Yasu31/Mini-Mobile-Manipulator/catkin_ws/src/mayfes/bot/img/0.jpg

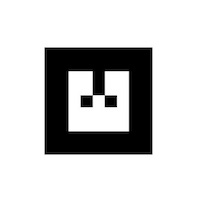
catkin_ws/src/mayfes/bot/img/0.jpg
