Yasu31/Mini-Mobile-Manipulator/catkin_ws/src/mayfes/bot/img/1.jpg

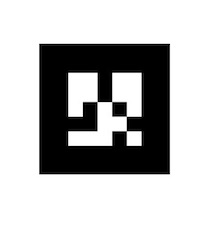
catkin_ws/src/mayfes/bot/img/1.jpg
