Yasu31/Mini-Mobile-Manipulator/img/ICS_connect.png

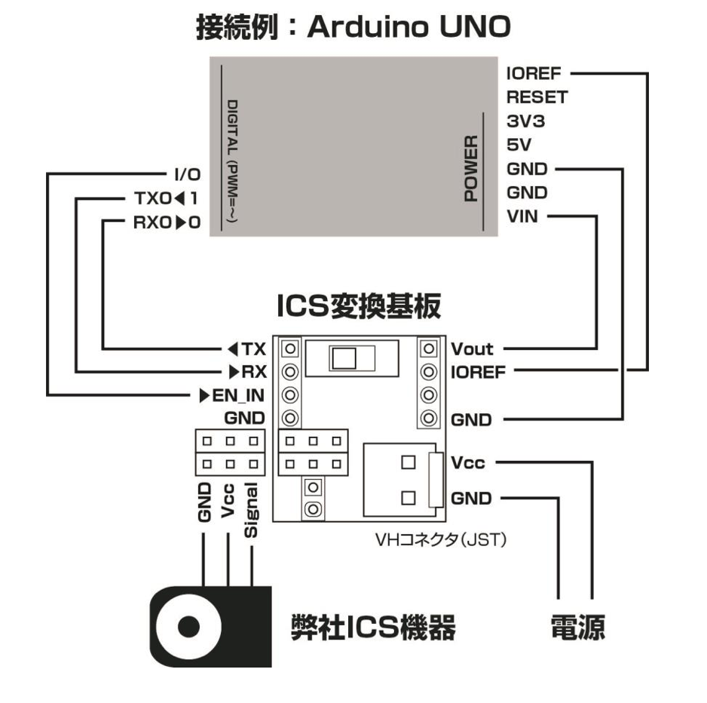
img/ICS_connect.png
