Yasu31/Mini-Mobile-Manipulator/img/IMG_5229.png

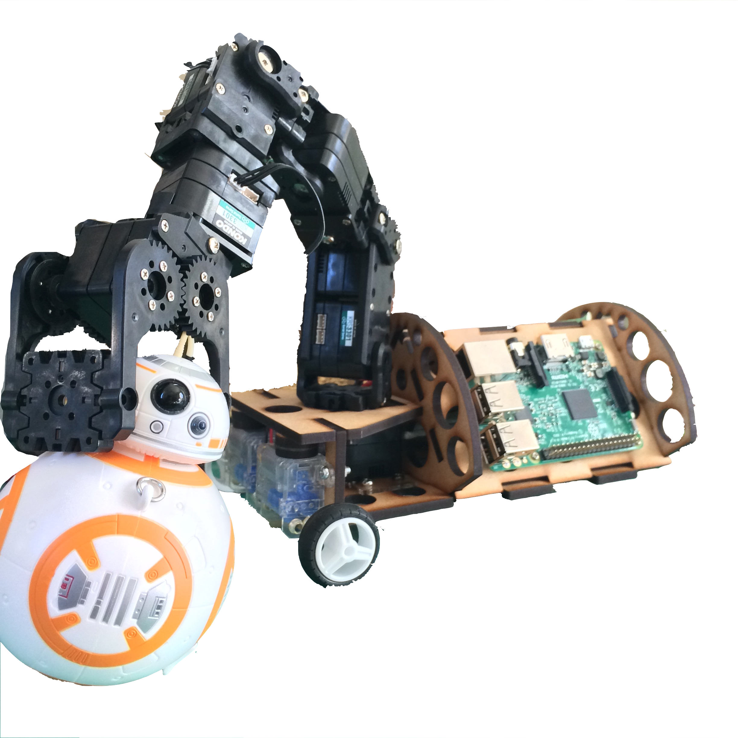
img/IMG_5229.png
