Yasu31/Mini-Mobile-Manipulator/img/modelC_render.png

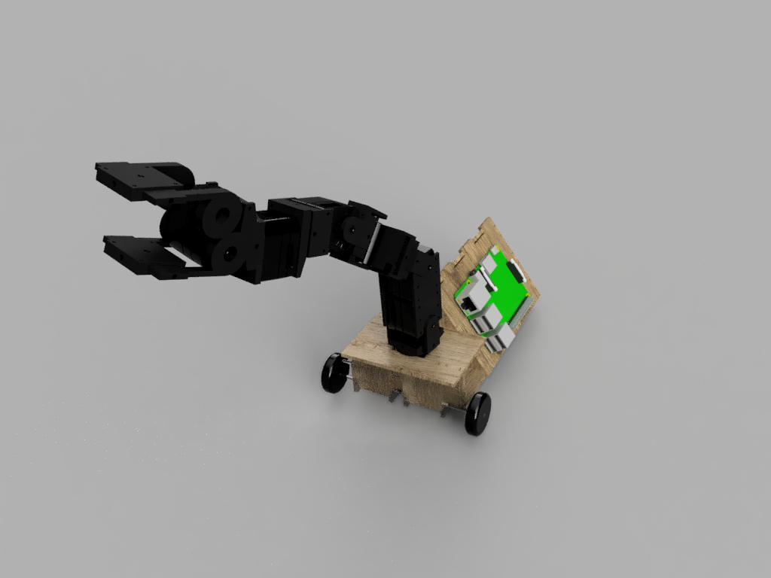
img/modelC_render.png
