Yasu31/Mini-Mobile-Manipulator/img/urdf_cad.png

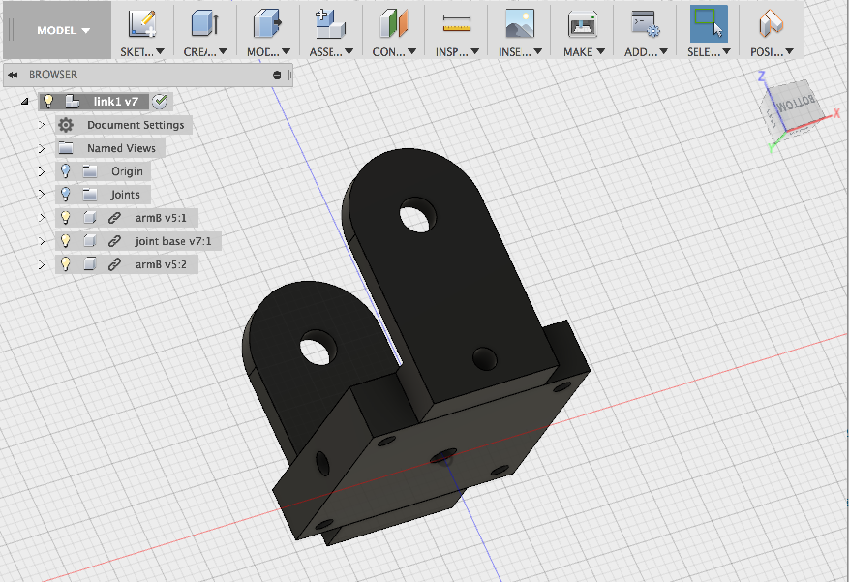
img/urdf_cad.png
