Yasu31/Mini-Mobile-Manipulator/Laser Cut Data/design C v1/rear wheel board.dxf

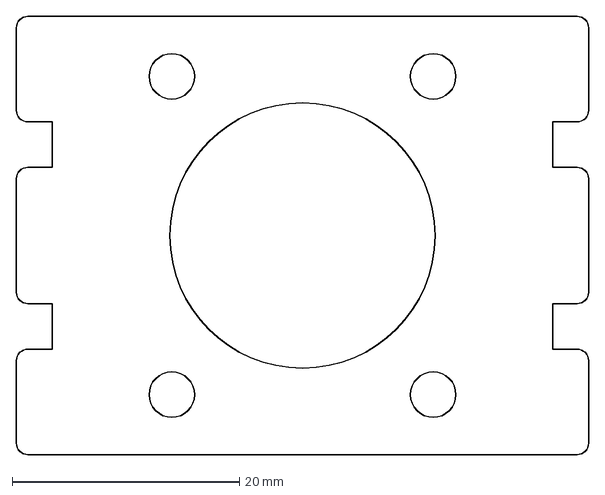
[picture p31: CAD file, 2017-12-26]
Laser Cut Data/design C v1/rear wheel board.dxf
50.3 x 38.6 mm
