Yasu31/Mini-Mobile-Manipulator/catkin_ws/src/mmm_description/meshes/Slink0.stl

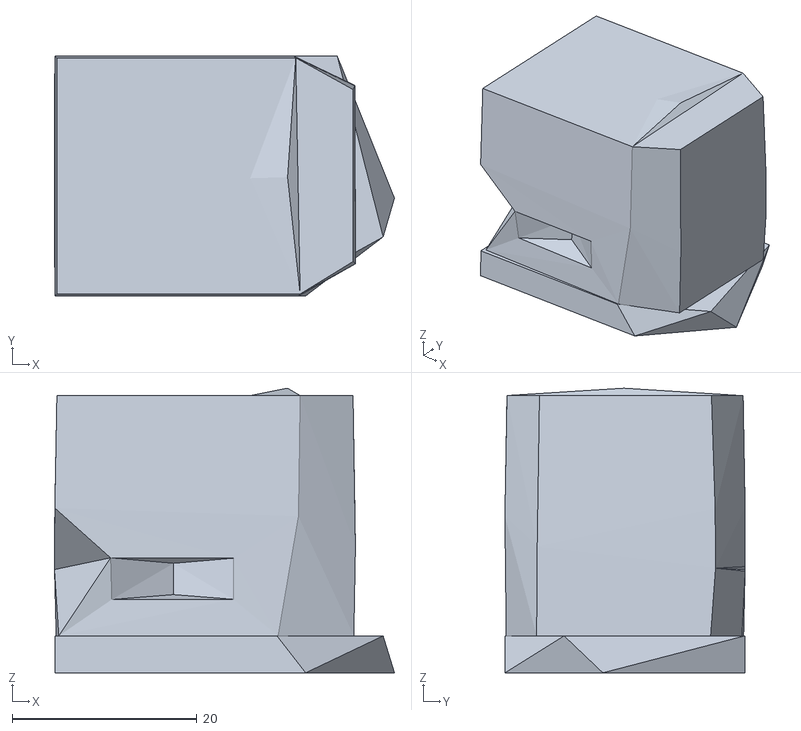
[picture p32: CAD file, 2018-01-10]
catkin_ws/src/mmm_description/meshes/Slink0.stl
36.8 x 26.0 x 30.8
