Yasu31/Mini-Mobile-Manipulator/Laser Cut Data/design C v1/middle board.dxf

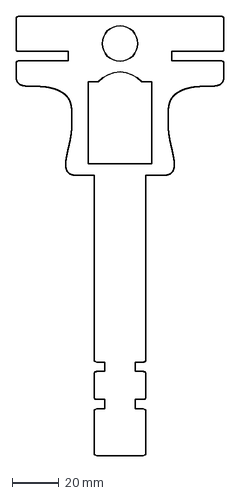
[picture p33: CAD file, 2017-12-26]
Laser Cut Data/design C v1/middle board.dxf
89.0 x 188.0 mm
