Yasu31/Mini-Mobile-Manipulator/catkin_ws/src/mmm_description/meshes/Slink7.stl

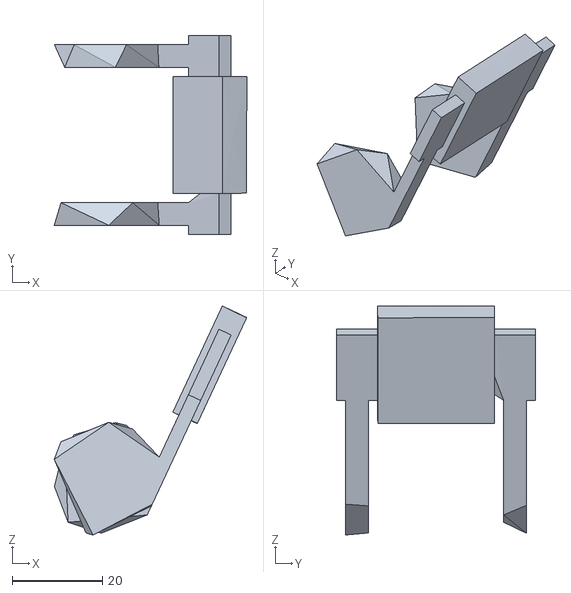
[picture p34: CAD file, 2018-01-10]
catkin_ws/src/mmm_description/meshes/Slink7.stl
42.7 x 44.0 x 50.7
