Yasu31/Mini-Mobile-Manipulator/Laser Cut Data/design C v1/diagonal board.dxf

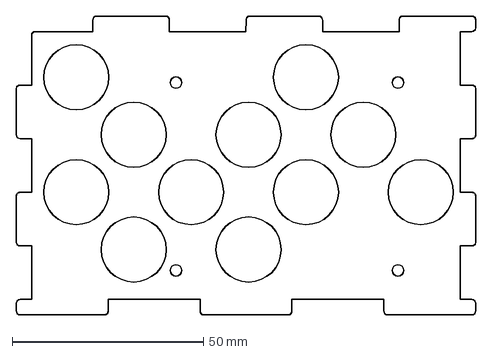
[picture p35: CAD file, 2017-12-26]
Laser Cut Data/design C v1/diagonal board.dxf
120.0 x 78.0 mm
