Yasu31/Mini-Mobile-Manipulator/catkin_ws/src/mmm_description/meshes/Slink5.stl

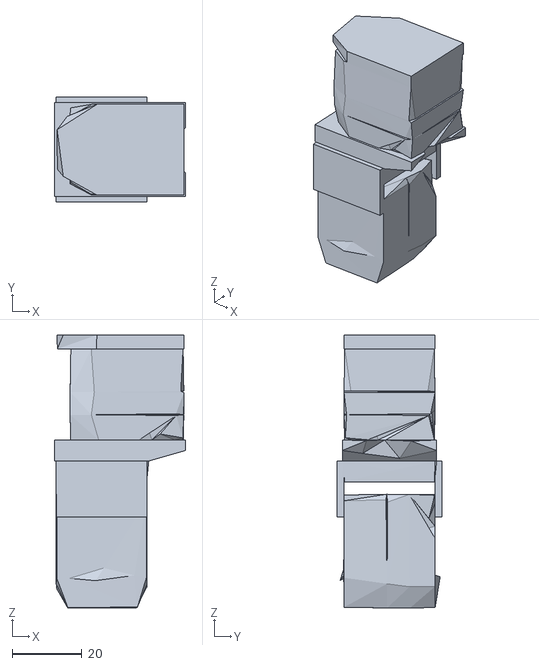
[picture p36: CAD file, 2018-01-10]
catkin_ws/src/mmm_description/meshes/Slink5.stl
37.5 x 30.0 x 78.0
