Yasu31/Mini-Mobile-Manipulator/catkin_ws/src/mmm_description/meshes/camera.stl

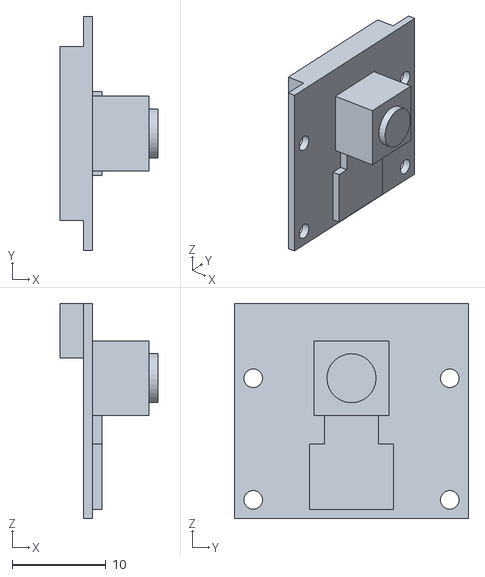
[picture p37: CAD file, 2018-01-08]
catkin_ws/src/mmm_description/meshes/camera.stl
10.5 x 25.0 x 23.0
