Yasu31/Mini-Mobile-Manipulator/catkin_ws/src/mmm_description/meshes/link7.stl

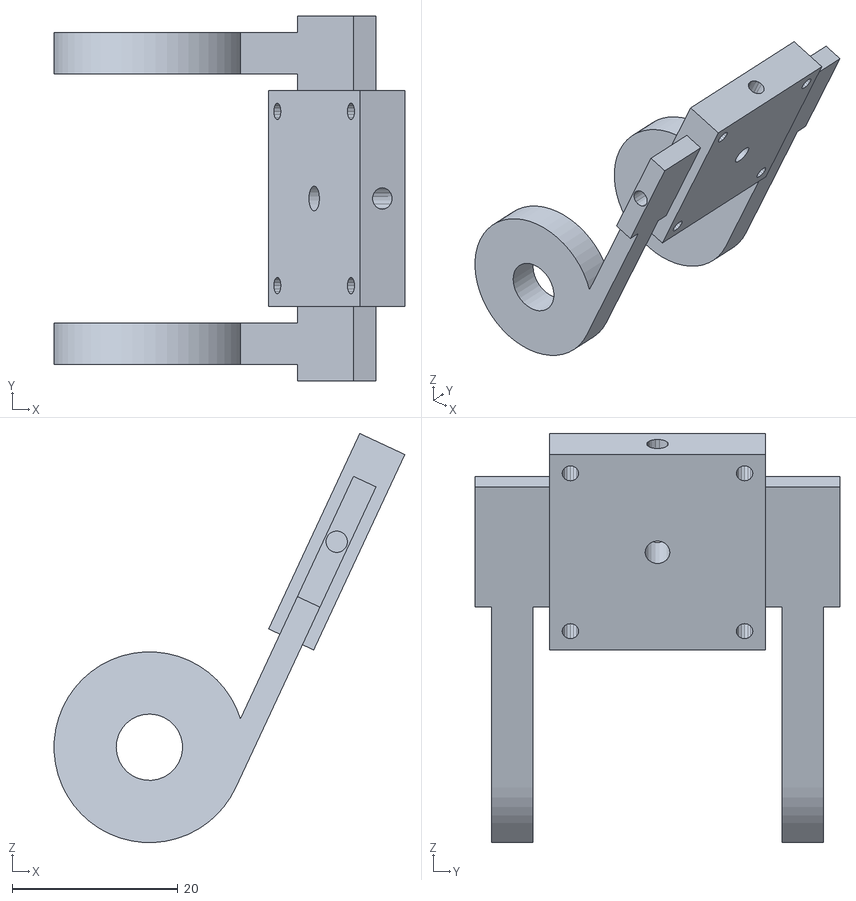
[picture p38: CAD file, 2018-01-02]
catkin_ws/src/mmm_description/meshes/link7.stl
42.3 x 44.0 x 49.3
