Yasu31/Mini-Mobile-Manipulator/catkin_ws/src/mmm_description/meshes/link6.stl

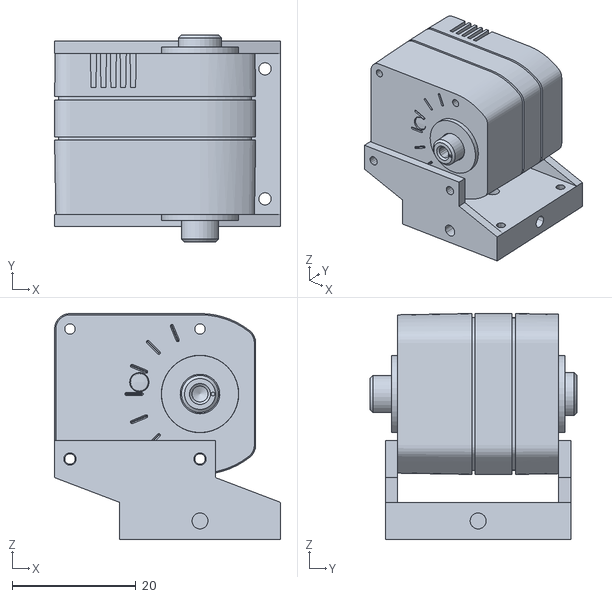
[picture p39: CAD file, 2018-01-02]
catkin_ws/src/mmm_description/meshes/link6.stl
36.5 x 33.5 x 36.5
