Yasu31/Mini-Mobile-Manipulator/catkin_ws/src/mmm_description/meshes/link2.stl

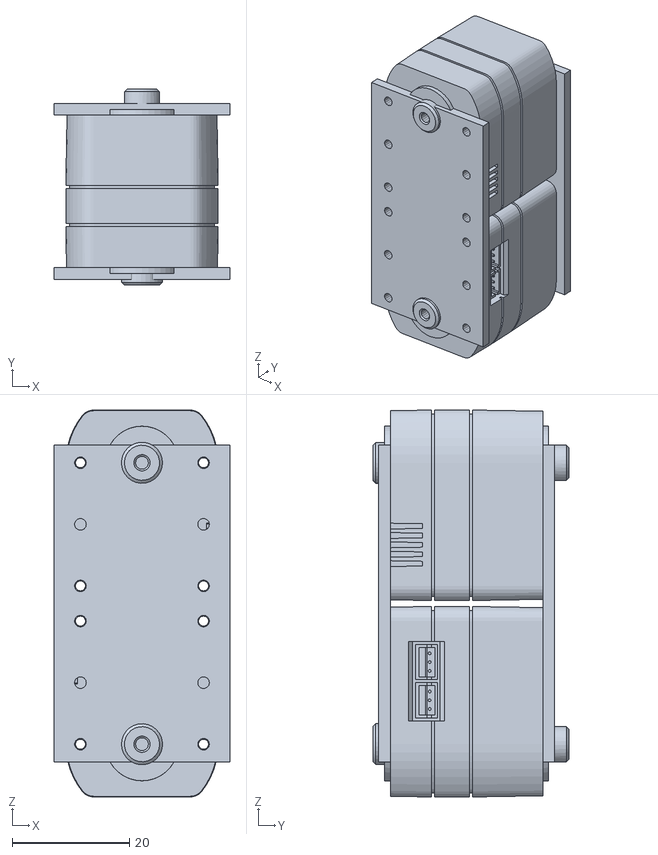
[picture p40: CAD file, 2017-12-29]
catkin_ws/src/mmm_description/meshes/link2.stl
30.0 x 33.5 x 66.0
