Yasu31/Mini-Mobile-Manipulator/catkin_ws/src/mmm_description/meshes/link4.stl

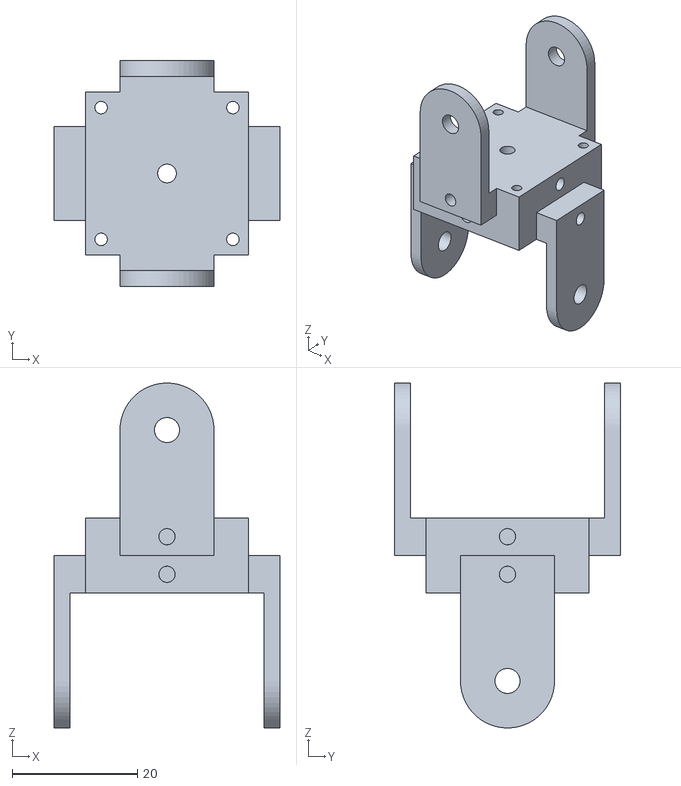
[picture p41: CAD file, 2017-12-29]
catkin_ws/src/mmm_description/meshes/link4.stl
36.0 x 36.0 x 55.0
