Yasu31/Mini-Mobile-Manipulator/catkin_ws/src/mmm_description/meshes/link5.stl

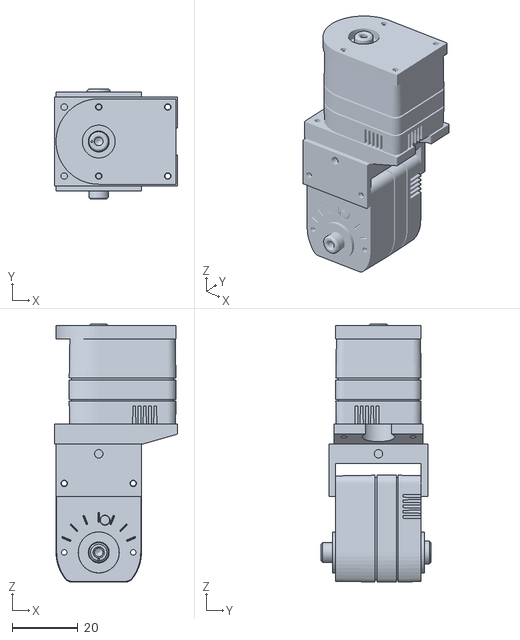
[picture p42: CAD file, 2017-12-29]
catkin_ws/src/mmm_description/meshes/link5.stl
37.5 x 33.5 x 78.5
