Yasu31/Mini-Mobile-Manipulator/catkin_ws/src/mmm_description/meshes/link3.stl

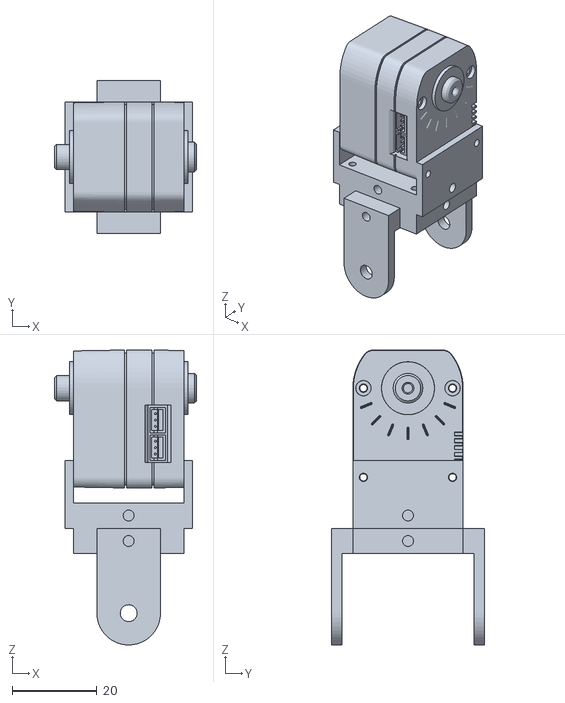
[picture p43: CAD file, 2017-12-29]
catkin_ws/src/mmm_description/meshes/link3.stl
33.5 x 36.0 x 69.5
