Yasu31/Mini-Mobile-Manipulator/catkin_ws/src/mmm_description/meshes/link1.stl

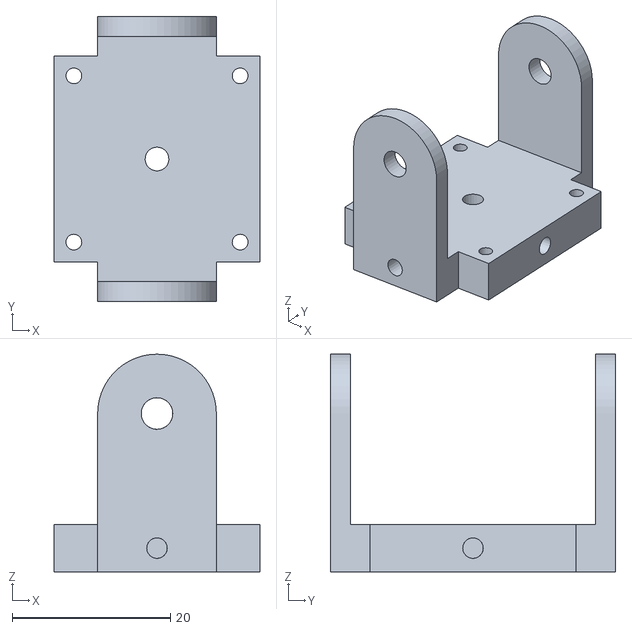
[picture p44: CAD file, 2017-12-27]
catkin_ws/src/mmm_description/meshes/link1.stl
26.0 x 36.0 x 27.5
