Yasu31/Mini-Mobile-Manipulator/catkin_ws/src/mmm_description/meshes/base.stl

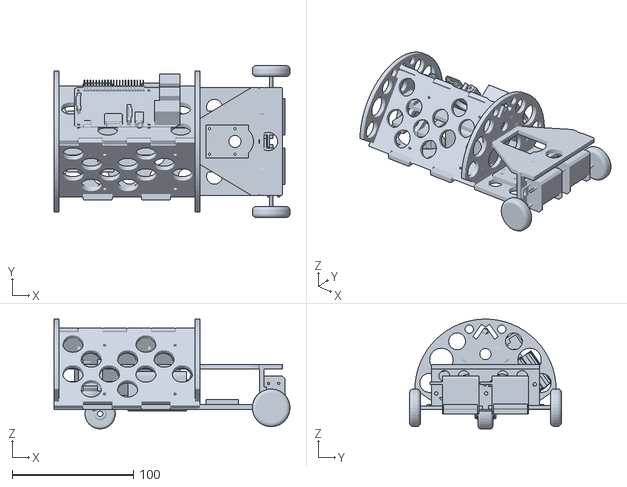
[picture p45: CAD file, 2017-12-27]
catkin_ws/src/mmm_description/meshes/base.stl
194.3 x 125.0 x 90.5
