Yasu31/Mini-Mobile-Manipulator/catkin_ws/src/mmm_description/meshes/link0.stl

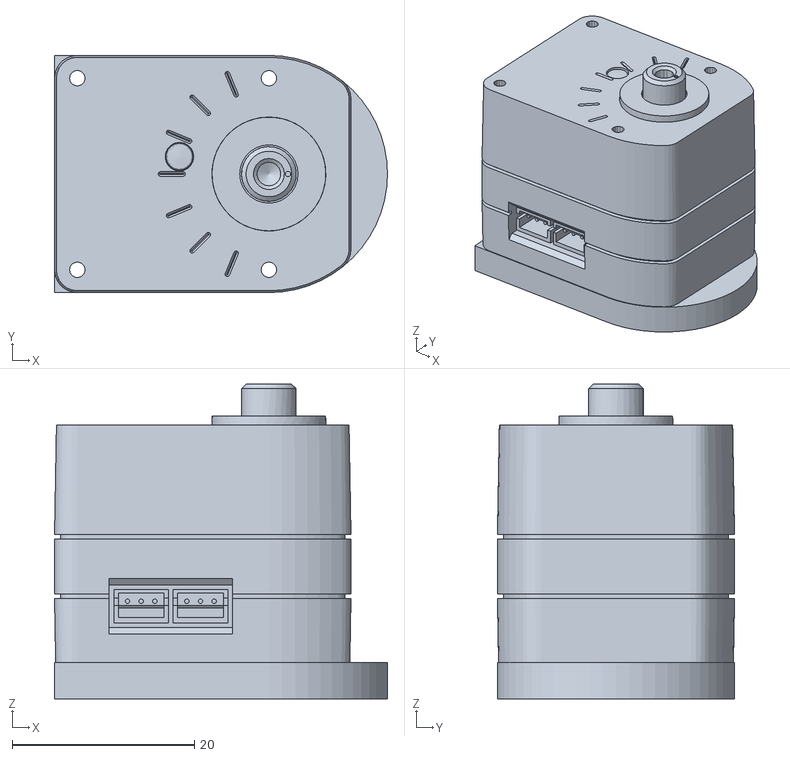
[picture p46: CAD file, 2017-12-27]
catkin_ws/src/mmm_description/meshes/link0.stl
36.5 x 26.0 x 34.5
