Yasu31/Mini-Mobile-Manipulator/Arduino Library/IcsClass_V100/IcsClass.cpp

/**
*	@file IcsClass.cpp
*	@brief ICS3.5/3.6 arduino library
*	@date	2016/11/01
*	@version 1.0.0
*	@copyright &copy; Kondo Kagaku Co.,Ltd. 2016
**/

#include "IcsClass.h"
#include "arduino.h"



/**
*	@brief コンストラクタ
*	@param[in] *serial ICSに設定するUART(HardwareSerial型のポインタ)
* @param[in] enpin 送受信切替えピンのピン番号
**/
IcsClass::IcsClass(HardwareSerial *serial,int enpin)
{
  icsSerial = serial;
  enPin = enpin;
}

/**
* @brief コンストラクタ
* @param[in] *serial ICSに設定するUART(HardwareSerial型のポインタ)
* @param[in] enpin 送受信切替えピンのピン番号
* @param[in] bandrate サーボの通信速度
* @param[in] timeout 受信タイムアウト(ms)

**/
IcsClass::IcsClass(HardwareSerial *serial, int enpin,long baudrate,int timeout)
{
  icsSerial = serial;
  enPin = enpin;
  baudRate = baudrate;
  timeOut = timeout;
  
}


/**
* @brief デストラクタ
* @post 使用していたのSerialを開放します
**/
IcsClass::~IcsClass()
{
  if (icsSerial)  //定義してあったらSerialを解放する
  {
    icsSerial->end();
  }
}



//初期設定 　void setup()へ　///////////////////////////////////////////////////////////////////////////////
/**
* @brief 通信の初期設定
* @retval true 通信設定完了
* @retval false 通信設定失敗
* @attention 通信速度、タイムアウトは事前に設定してある事
**/
bool IcsClass::begin()
{
  if (!icsSerial)
  {
    return false;
  }

  icsSerial->begin(baudRate, SERIAL_8E1);
  icsSerial->setTimeout(timeOut);
  pinMode(enPin, OUTPUT);
  enLow();

  return true;
}

/**
* @brief 通信の初期設定
* @param[in] baudrate ICSの通信速度(115200,625000,1250000(1.25M)bps)
* @param[in] timeout 受信タイムアウト(ms)
* @retval true 通信設定完了
* @retval false 通信設定失敗
* @attention UARTピンおよび送受信切替えピンは設定してある事
**/
bool IcsClass::begin(long baudrate,int timeout)
{
  baudRate =  baudrate;
  timeOut  = timeout;
  begin();
}

/**
* @brief 通信の初期設定
* @param[in] *serial ICSに設定するUART(HardwareSerial型のポインタ)
* @param[in] enpin 送受信切替えピンのピン番号
* @param[in] baudrate ICSの通信速度(115200,625000,1250000(1.25M)bps)
* @param[in] timeout 受信タイムアウト(ms)
* @retval true 通信設定完了
* @retval false 通信設定失敗
**/
bool IcsClass::begin(HardwareSerial *serial,int enpin,long baudrate,int timeout)
{
  icsSerial = serial;
  enPin = enpin;
  baudRate =  baudrate;
  timeOut  = timeout;
  begin();
}


//イネーブルピン　Hi (送信）////////////////////////////////////////////////////////////////////////////////
/**
* @brief 送受信切替えピンをHにします
**/
inline void IcsClass::enHigh()
{
  digitalWrite(enPin, HIGH);
}


//イネーブルピン　Low (受信) ///////////////////////////////////////////////////////////////////////////////
/**
* @brief 送受信切替えピンをLにします
**/
inline void IcsClass::enLow()
{
  digitalWrite(enPin, LOW);
}


//データ送受信 /////////////////////////////////////////////////////////////////////////////////////////////
/**
* @brief ICS通信の送受信
* @param[in,out] *txBuf
* @param[in] txLen
* @param[out] *rxBuf 受信格納バッファ
* @param[in] rxLen  受信データ数
* @retval true 通信成功
* @retval false 通信失敗
* @attention 送信データ数、受信データ数はコマンドによって違うので注意する
**/
bool IcsClass::synchronize(byte *txBuf, byte txLen, byte *rxBuf, byte rxLen)
{
  int rxSize; //受信数
  byte buff;
  int i;
  //シリアル初期化確認
  if (icsSerial == false)return false;

  icsSerial->flush(); //待つ
  enHigh(); //送信切替
  icsSerial->write(txBuf, txLen);
  icsSerial->flush();   //待つ
  while (icsSerial->available() > 0) //受信バッファを消す
  {
    buff = icsSerial->read();
  }
  enLow();  //受信切替


  rxSize = icsSerial->readBytes(rxBuf, rxLen);

  if (rxSize != rxLen) //受信数確認
  {
    return false;
  }
  return true;
}


//サーボID範囲 /////////////////////////////////////////////////////////////////////////////////////////////
/**
* @brief サーボIDが範囲内か見る
* @param[in] id
* @return 送られてきたid
* @retval 0xFF 範囲外
**/
byte IcsClass::idMax(byte id)
{
  if (id < MIN_ID) {
    id = 0xFF;
  }
  if (id > MAX_ID) {
    id = 0xFF;
  }
  return id;
}



//サーボ可動範囲　パラメータ範囲　リミット設定 //////////////////////////////////////////////////////////////
/**
* @brief ポジションデータの最大、最小値の範囲に収める
* @param[in] maxPos 最大値
* @param[in] minPos 最小値
* @param[in,out] val 現在値
* @return リミットがかかったポジションデータ
**/
bool IcsClass::maxMin(int maxPos, int minPos, int val)
{
  if (val > maxPos) {
    return false;
  }
  if (val < minPos) {
    return false;
  }
  return true;
}



//角度変換　角度からPOSへ////////////////////////////////////////////////////////////////////////////////////
/**
* @brief 角度データ(float型)をポジションデータに変換
* @param[in] deg 角度(deg)(float型)
* @return ポジションデータ
* @retval -1 範囲外
**/
int IcsClass::degPos(float deg)
{
  if (deg > MAX_DEG) {
    return -1;
  }
  if (deg < MIN_DEG) {
    return -1;
  }
  int pos = deg * 29.633;
  pos = pos + 7500;
  return pos;
}


//角度変換　POSから角度へ////////////////////////////////////////////////////////////////////////////////////
/**
* @brief ポジションデータを角度データ(float型)に変換
* @param[in] pos ポジションデータ
* @return 角度(deg)(float型)
* @retval #ANGLE_F_FALSE  正方向範囲外
* @retval -#ANGLE_F_FALSE (0x8000) 負方向範囲外
**/
float IcsClass::posDeg(int pos)
{
  pos = pos - 7500;
  float deg = pos  / 29.633;

  if (deg > MAX_DEG) {
    return ANGLE_F_FALSE;
  }
  if (deg < MIN_DEG) {
    return -ANGLE_F_FALSE;
  }

  return deg;
}


//角度変換　x100 角度からPOSへ///////////////////////////////////////////////////////////////////////////////
/**
* @brief 角度データx100(int型)をポジションデータに変換
* @param[in] deg 角度(deg x100)(int型)
* @return 変換されたポジションデータ
* @retval -1 範囲外
**/
int IcsClass::degPos100(int deg)
{
  if (deg > MAX_100DEG) {
    return -1 ;
  }
  if (deg < MIN_100DEG) {
    return -1;
  }
  long a  = ((long)deg * 2963) / 10000;
  int pos = a + 7500;
  return pos;
}


//角度変換　x100 POSから角度へ///////////////////////////////////////////////////////////////////////////////
/**
* @brief ポジションデータを角度データ(int型)に変換
* @param[in] pos ポジションデータ
* @return 角度(deg x100)(int型)
* @retval #ANGLE_I_FALSE 正方向範囲外
* @retval -#ANGLE_I_FALSE 負方向範囲外
**/
int IcsClass::posDeg100(int pos)
{
  long a = pos - 7500;
  int deg = (a * 1000) / 296;

  if (deg > MAX_100DEG) {
    return ANGLE_I_FALSE;
  }
  if (deg < MIN_100DEG) {
    return -ANGLE_I_FALSE;
  }
  return deg;
}



//サーボ角度セット //////////////////////////////////////////////////////////////////////////////////////////
/**
* @brief サーボモータの角度を変更します
* @param[in] id サーボモータのID番号
* @param[in] pos ポジションデータ
* @return ポジションデータ
* @retval -1 範囲外、通信失敗
**/
int IcsClass::setPos(byte id, unsigned int pos)
{
  byte txCmd[3];
  byte rxCmd[3];
  unsigned int rePos;
  bool flg;
  if ((id != idMax(id)) || ( ! maxMin(MAX_POS, MIN_POS, pos)) ) //範囲外の時
  {
    return ICS_FALSE;
  }

  txCmd[0] = 0x80 + id;               // CMD
  txCmd[1] = ((pos >> 7) & 0x007F);   // POS_H
  txCmd[2] = (pos & 0x007F);          // POS_L

  //送受信
  flg = synchronize(txCmd, sizeof txCmd, rxCmd, sizeof rxCmd);
  if (flg == false)
  {
    return ICS_FALSE;
  }

  rePos = ((rxCmd[1] << 7) & 0x3F80) + (rxCmd[2] & 0x007F);

  return rePos;

}



//サーボ フリーモード ///////////////////////////////////////////////////////////////////////////////////////
/**
* @brief サーボモータをフリー(脱力)状態にします
* @param[in] id サーボモータのID番号
* @return ポジションデータ
* @retval -1 範囲外、通信失敗
**/
int IcsClass::setFree(byte id)
{
  byte txCmd[3];
  byte rxCmd[3];
  unsigned int rePos;
  bool flg;

  if (id != idMax(id)) //範囲外の時
  {
    return ICS_FALSE;
  }

  txCmd[0] = 0x80 + id;    // CMD
  txCmd[1] = 0;
  txCmd[2] = 0;

  //送受信
  flg = synchronize(txCmd, sizeof txCmd, rxCmd, sizeof rxCmd);
  if (flg == false)
  {
    return ICS_FALSE;
  }

  rePos = ((rxCmd[1] << 7) & 0x3F80) + (rxCmd[2] & 0x007F);

  return rePos;

}




//ストレッチ値書込み　1～127 ////////////////////////////////////////////////////////////////////////////////
/**
* @brief サーボモータのストレッチ(保持力)の値を書き込みます
* @param[in] id サーボモータのID番号
* @param[in] strc ストレッチのデータ(1～127)
* @return 書き込んだストレッチのデータ
* @retval -1 通信失敗
* @note ストレッチ書込 1～127  1(弱）      127(強）
**/
int IcsClass::setStrc(byte id, unsigned int strc)
{
  byte txCmd[3];
  byte rxCmd[3];
  unsigned int reData;
  bool flg;

  if ((id != idMax(id)) || ( ! maxMin(MAX_127, MIN_1, strc)) ) //範囲外の時
  {
    return ICS_FALSE;
  }

  txCmd[0] = 0xC0 + id;    // CMD
  txCmd[1] = 0x01;         // SC ストレッチ
  txCmd[2] = strc;         // ストレッチ


  //送受信
  flg = synchronize(txCmd, sizeof txCmd, rxCmd, sizeof rxCmd);
  if (flg == false)
  {
    return ICS_FALSE;
  }
  reData = rxCmd[2];

  return reData;

}



//スピード値書込み　1～127 //////////////////////////////////////////////////////////////////////////////////
/**
* @brief サーボモータのスピード(出力)を変更します
* @param[in] id サーボモータのID番号
* @param[in] spd スピードのデータ(1～127)
* @return 書き込んだスピードのデータ
* @retval -1 通信失敗
* @note スピード書込   1～127  1(遅い)     127(速い)
**/
int IcsClass::setSpd(byte id, unsigned int spd)
{
  byte txCmd[3];
  byte rxCmd[3];
  unsigned int reData;
  bool flg;

  if ((id != idMax(id)) || ( ! maxMin(MAX_127, MIN_1, spd)) ) //範囲外の時
  {
    return ICS_FALSE;
  }

  txCmd[0] = 0xC0 + id;      // CMD
  txCmd[1] = 0x02;           // SC スピード
  txCmd[2] = spd;            // スピード

  //送受信
  flg = synchronize(txCmd, sizeof txCmd, rxCmd, sizeof rxCmd);
  if (flg == false)
  {
    return ICS_FALSE;
  }

  reData = rxCmd[2];

  return reData;

}




//電流リミット値書込み　1～63 ///////////////////////////////////////////////////////////////////////////////
/**
* @brief サーボモータの電流リミット（電流制限）値を変更します
* @param[in] id サーボモータのID番号
* @param[in] curlim 電流値のデータ
* @return サーボモータの電流リミット値
* @retval -1 通信失敗
* @note 電流制限値書込 1～63   1(低い)     63 (高い)
**/
int IcsClass::setCur(byte id, unsigned int curlim)
{
  byte txCmd[3];
  byte rxCmd[3];
  unsigned int reData;
  bool flg;

  if ((id != idMax(id)) || ( ! maxMin(MAX_63, MIN_1, curlim)) ) //範囲外の時
  {
    return ICS_FALSE;
  }

  txCmd[0] = 0xC0 + id;                     // CMD
  txCmd[1] = 0x03;                          // SC 電流値
  txCmd[2] = curlim;                        // 電流リミット値


  //送受信
  flg = synchronize(txCmd, sizeof txCmd, rxCmd, sizeof rxCmd);
  if (flg == false)
  {
    return ICS_FALSE;
  }

  reData = rxCmd[2];

  return reData;

}




//温度リミット値書込み 　1～127 /////////////////////////////////////////////////////////////////////////////
/**
* @brief サーボモータの温度リミット（温度制限）値を変更します
* @param[in] id サーボモータのID番号
* @param[in] tmplim 温度リミット値のデータ
* @return サーボモータの温度リミット値
* @retval -1 通信失敗
* @note 温度上限書込   1～127  127(低温）  1(高温)
**/
int IcsClass::setTmp(byte id, unsigned int tmplim)
{
  byte txCmd[3];
  byte rxCmd[3];
  unsigned int reData;
  bool flg;
//  if (id != idMax(id)) //範囲外の時
//  {
//    return ICS_FALSE;
//  }
//  tmplim = maxMin(MAX_127, MIN_1, tmplim);   //入力値範囲

  if ((id != idMax(id)) || ( ! maxMin(MAX_127, MIN_1, tmplim)) ) //範囲外の時
  {
    return ICS_FALSE;
  }


  txCmd[0] = 0xC0 + id;                      // CMD
  txCmd[1] = 0x04;                           // SC 温度値
  txCmd[2] = tmplim;                         // 温度リミット値

  //送受信
  flg = synchronize(txCmd, sizeof txCmd, rxCmd, sizeof rxCmd);
  if (flg == false)
  {
    return ICS_FALSE;
  }

  reData = rxCmd[2];

  return reData;

}


//ストレッチ値読出し　1～127 ////////////////////////////////////////////////////////////////////////////////
/**
* @brief サーボモータのストレッチ(保持力)の値を読み込みます
* @param[in] id サーボモータのID番号
* @return 読み込んだストレッチのデータ
* @retval -1 通信失敗
* @note ストレッチ読込    1～127  1(弱）      127(強）
**/
int IcsClass::getStrc(byte id)
{
  byte txCmd[2];
  byte rxCmd[3];
  unsigned int reData;
  bool flg;
  //id = idMax(id);          //ID範囲
  if (id != idMax(id)) //範囲外の時
  {
    return ICS_FALSE;
  }
  txCmd[0] = 0xA0 + id;    // CMD
  txCmd[1] = 0x01;         // SC ストレッチ


  //送受信
  flg = synchronize(txCmd, sizeof txCmd, rxCmd, sizeof rxCmd);
  if (flg == false)
  {
    return ICS_FALSE;
  }

  reData = rxCmd[2];

  return reData;

}




//スピード値読出し　1～127 //////////////////////////////////////////////////////////////////////////////////
/**
* @brief サーボモータのスピード(出力)を読み込みます
* @param[in] id サーボモータのID番号
* @return 読み込んだスピードのデータ
* @retval -1 通信失敗
* @note スピード読込      1～127  1(遅い)     127(速い)
**/
int IcsClass::getSpd(byte id)
{
  byte txCmd[2];
  byte rxCmd[3];
  unsigned int reData;
  bool flg;
  if (id != idMax(id)) //範囲外の時
  {
    return ICS_FALSE;
  }
  txCmd[0] = 0xA0 + id;    // CMD
  txCmd[1] = 0x02;         // SC スピード


  //送受信
  flg = synchronize(txCmd, sizeof txCmd, rxCmd, sizeof rxCmd);
  if (flg == false)
  {
    return ICS_FALSE;
  }

  reData = rxCmd[2];

  return reData;

}



//電流値読出し　正転時0～63、逆転時64～127 //////////////////////////////////////////////////////////
/**
* @brief サーボモータの現在の電流値を読み込みます
* @param[in] id サーボモータのID番号
* @return サーボモータの現在の電流値
* @retval -1 通信失敗
* @note 電流値読込      正転時0～63、逆転時64～127
**/
int IcsClass::getCur(byte id)
{
  byte txCmd[2];
  byte rxCmd[3];
  unsigned int reData;
  bool flg;
  if (id != idMax(id)) //範囲外の時
  {
    return ICS_FALSE;
  }
  txCmd[0] = 0xA0 + id;    // CMD
  txCmd[1] = 0x03;         // SC 電流値


  //送受信
  flg = synchronize(txCmd, sizeof txCmd, rxCmd, sizeof rxCmd);
  if (flg == false)
  {
    return ICS_FALSE;
  }

  reData = rxCmd[2];

  return reData;

}




//温度値読出し　1～127 ///////////////////////////////////////////////////////////////////////////////
/**
* @brief サーボモータの現在の温度値を読み込みます
* @param[in] id サーボモータのID番号
* @return サーボモータの現在の温度値
* @retval -1 通信失敗
* @note 現在温度読込	0(高温) ～ 127(低温
**/
int IcsClass::getTmp(byte id)
{
  byte txCmd[2];
  byte rxCmd[3];
  unsigned int reData;
  bool flg;
  if (id != idMax(id)) //範囲外の時
  {
    return ICS_FALSE;
  }
  txCmd[0] = 0xA0 + id;    // CMD
  txCmd[1] = 0x04;         // SC 温度値


  //送受信
  flg = synchronize(txCmd, sizeof txCmd, rxCmd, sizeof rxCmd);
  if (flg == false)
  {
    return ICS_FALSE;
  }

  reData = rxCmd[2];

  return reData;

}


//現在値読出し　※ICS3.6以降で有効 //////////////////////////////////////////////////////////////////////////
/**
* @brief サーボモータの現在のポジションデータを読み込みます
* @param[in] id サーボモータのID番号
* @return 指定したIDの現在のポジションデータ
* @retval -1 通信失敗
* @attention ICS3.6から有効です。ICS3.5のサーボモータに送った場合は返事を返しません
**/
int IcsClass::getPos(byte id)
{
  byte txCmd[2];
  byte rxCmd[4];
  unsigned int reData;
  bool flg;
  if (id != idMax(id)) //範囲外の時
  {
    return ICS_FALSE;
  }
  txCmd[0] = 0xA0 + id;    // CMD
  txCmd[1] = 0x05;         // 角度読出し


  //送受信
  flg = synchronize(txCmd, sizeof txCmd, rxCmd, sizeof rxCmd);
  if (flg == false)
  {
    return ICS_FALSE;
  }

  reData = ((rxCmd[2] << 7) & 0x3F80) + (rxCmd[3] & 0x007F);

  return reData;

}



//KRR5全ボタン読出し ////////////////////////////////////////////////////////////////////////////////////////
/**
* @brief KRRが受信しているボタンのデータを取得します
* @return #KRR_BUTTON を参照
* @retval -1 通信失敗
**/
unsigned short IcsClass::getKrrButton()
{
  byte txCmd[4];
  byte rxCmd[8];
  unsigned short btn;
  bool flg;

  txCmd[0] = 0xBF;   // CMD
  txCmd[1] = 0x7F;   // SC 受信データ読込
  txCmd[2] = 0x00;   //ADDR
  txCmd[3] = 0x02;   //BYTE


  //送受信
  flg = synchronize(txCmd, sizeof txCmd, rxCmd, sizeof rxCmd);
  if (flg == false)
  {
    return KRR_BUTTON_FALSE;
  }

  //ボタンデータ
  btn = ((rxCmd[4] << 4) & 0xF0) + (rxCmd[5] & 0x0F);
  btn = (btn << 8 | ((rxCmd[6] << 4) & 0xF0) + (rxCmd[7] & 0x0F));

  return btn;

}


//KRR5 PAアナログ読出し /////////////////////////////////////////////////////////////////////////////////////
/**
* @brief KRRが受信している指定したアナログポート(PA)のデータを取得します
* @param[in] paCh アナログポートの番号
* @return 指定したアナログポートのデータ
* @retval -1 通信失敗
* @attention KRC5のアナログポートは1～4になります
**/
int IcsClass::getKrrAnalog(int paCh)
{
  byte txCmd[4];
  byte rxCmd[6];
  int adData;
  bool flg;

  if (1 > paCh || paCh > 4) //ADがない場合は-1を返す
  {
    return false;
  }

  txCmd[0] = 0xBF;   // CMD
  txCmd[1] = 0x7F;   // SC 受信データ読込
  txCmd[2] = (1 + paCh);   //ADDR
  txCmd[3] = 0x01;   //BYTE


  //送受信
  flg = synchronize(txCmd, sizeof txCmd, rxCmd, sizeof rxCmd);
  if (flg == false)
  {
    return ICS_FALSE;
  }

  adData =  ((rxCmd[4] << 4) & 0xF0) + (rxCmd[5] & 0x0F);

  return adData;
}


//KRR5 全読出し /////////////////////////////////////////////////////////////////////////////////////////////
/**
* @brief KRRが受信しているボタンデータおよびアナログポート(PA)のデータをすべて取得します
* @param[out] button ボタンデータ(#KRR_BUTTON を参照)
* @param[out] adData 4ch分のアナログデータ
* @retval ture 通信成功
* @retval false 通信失敗
* @attention KRC5のアナログポートは1～4になります
* @attention 配列サイズは4固定です
**/
bool IcsClass::getKrrAllData(unsigned short *button,int adData[4])
{
  byte txCmd[4];
  byte rxCmd[18];
  unsigned short btn;
  bool flg;

  txCmd[0] = 0xBF;   // CMD
  txCmd[1] = 0x7F;   // SC 受信データ読込
  txCmd[2] = 0x00;   //ADDR
  txCmd[3] = 0x07;   //BYTE
  ;
  //送受信
  flg = synchronize(txCmd, sizeof txCmd, rxCmd, sizeof rxCmd);
  if (flg == false)
  {
    return false;
  }

  //ボタンデータ
  btn = ((rxCmd[4] << 4) & 0xF0) + (rxCmd[5] & 0x0F);
  btn = (btn << 8 | ((rxCmd[6] << 4) & 0xF0) + (rxCmd[7] & 0x0F));
  *button = btn;


  //アナログデータ
  for (int i = 0; i < 4; i++)
  {
    adData[i] = ((rxCmd[8 + i * 2] << 4) & 0xF0) + (rxCmd[9 + i * 2] & 0x0F);
  }
  return true;
}
