Yasu31/Mini-Mobile-Manipulator/Arduino Library/IcsClass_V100/examples/KrrAnalog/KrrAnalog.ino

//
//  @file KrrAnalog.ino
//  @brief KRR get Analog sample 
//  @author Kondo Kagaku Co.,Ltd.
//  @date 2016/12/27
//
//  KRR(受信機)に送られてきているアナログデータを取得します
//  アナログデータをもとにID:0のサーボモータを動かします。
//

#include <IcsClass.h>

const int enpin = 2;
const long baudrate = 115200;
const int timeout = 5;
IcsClass krs(&Serial,enpin,baudrate ,timeout);  //インスタンス＋ENピン(2番ピン)およびUARTの指定
//IcsClass krs(&Serial,2,115200,5);  //インスタンス＋ENピン(2番ピン)およびUARTの指定

void setup() {
  // put your setup code here, to run once:
   krs.begin();  //サーボモータの通信初期設定
  
}

void loop() {

   int analogData;
   int sendpos;

   analogData = krs.getKrrAnalog(1);        //PA1に接続されているアナログデータを読み取る
   if(analogData != krs.ICS_FALSE)  //受信が成功しているか判定
   {
    sendpos = 7500 + ((analogData-64)*62);  //
                                            // 受信データ - 64(7bit/2) <= 中央値からどれくらい離れているか計算
                                            //　　　　　　 ;        *62   <= 4000(ポジションは±4000)/64 = 62.5　だが、切り捨てて62
                                            // 7500 + (      ;            ) <= サーボモータの0点からの角度に変換                                            
    krs.setPos(0,sendpos);                  //ID:0に計算した値を送る
   }
   else
   {
    //通信に失敗してた時の処理
    delay(1000);
   }
  
    delay(10);    //KRR5は10ms以下の応答にはついていけないので待つ
}
